shemalperera/RFID_handhed_reader/Images/enclosure/enclosure_bottom.png

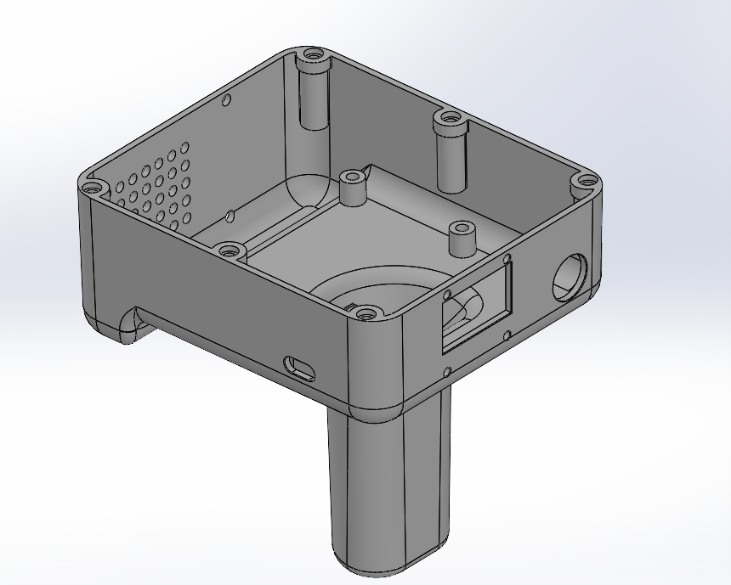
Images/enclosure/enclosure_bottom.png
