shemalperera/RFID_handhed_reader/Images/enclosure/enclosure_hand_sketch.png

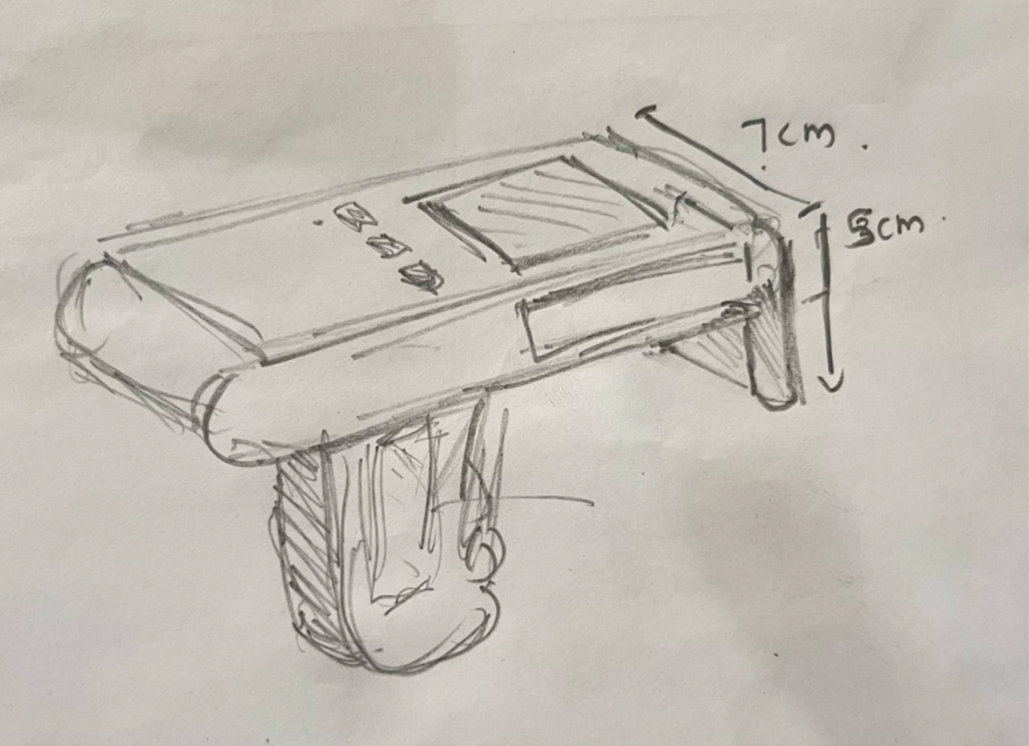
Images/enclosure/enclosure_hand_sketch.png
