shemalperera/RFID_handhed_reader/Images/enclosure/enclosure_lid.png

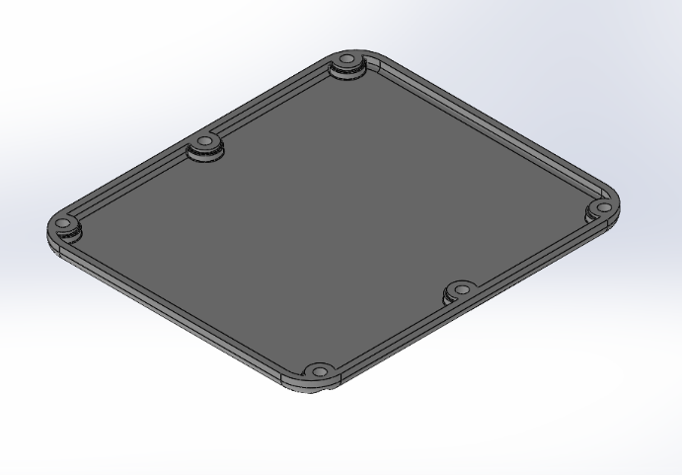
Images/enclosure/enclosure_lid.png
