shemalperera/RFID_handhed_reader/Images/enclosure/mold_bottom.png

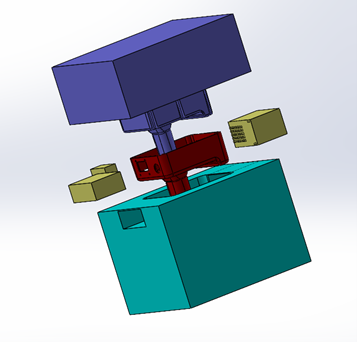
Images/enclosure/mold_bottom.png
