shemalperera/RFID_handhed_reader/Images/enclosure/mold_lid.png

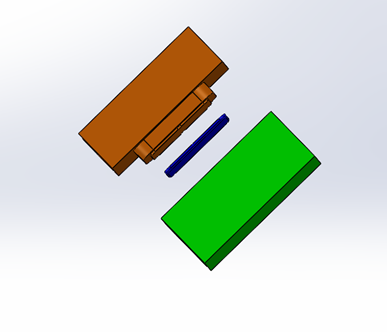
Images/enclosure/mold_lid.png
