shemalperera/RFID_handhed_reader/Images/pcb/main_pcb_front.jpg

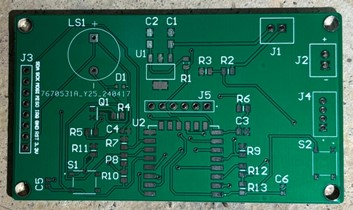
Images/pcb/main_pcb_front.jpg
