shemalperera/RFID_handhed_reader/Images/pcb/main_pcb_rear.jpg

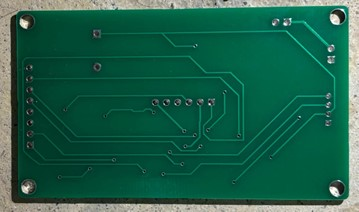
Images/pcb/main_pcb_rear.jpg
