shemalperera/RFID_handhed_reader/Images/pcb/PCB layout.png

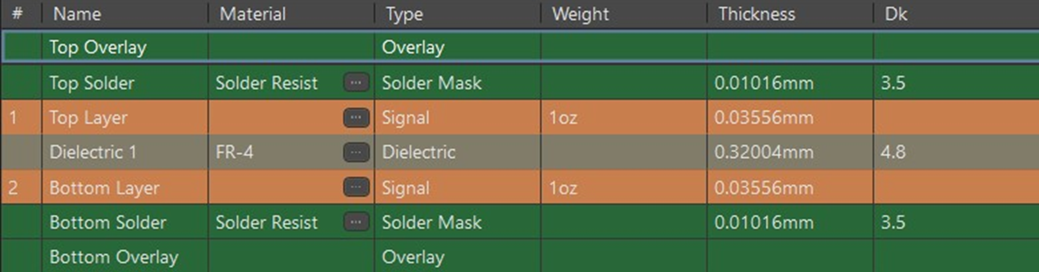
Images/pcb/PCB layout.png
