shemalperera/RFID_handhed_reader/Images/pcb/rfid_bottom_layer.png

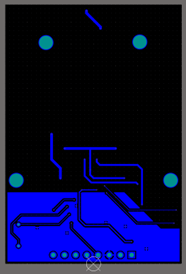
Images/pcb/rfid_bottom_layer.png
