shemalperera/RFID_handhed_reader/Images/pcb/rfid_pcb_rear.jpg

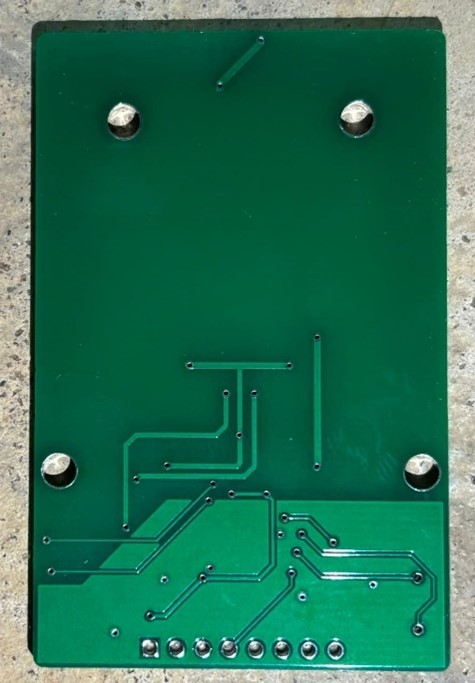
Images/pcb/rfid_pcb_rear.jpg
