shemalperera/RFID_handhed_reader/Images/pcb/rfid_pcb_top.jpg

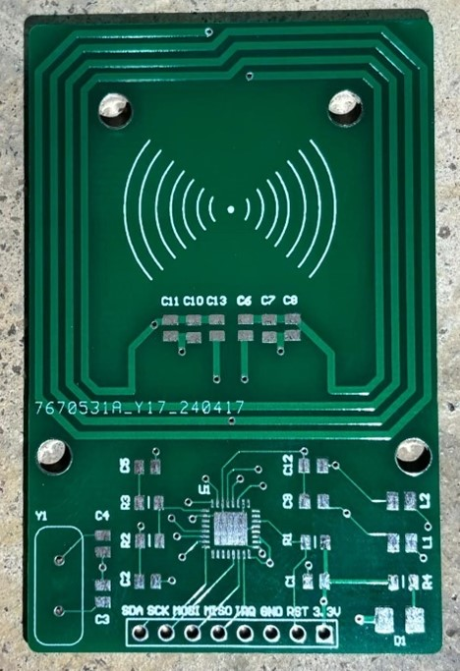
Images/pcb/rfid_pcb_top.jpg
