shemalperera/RFID_handhed_reader/Images/pcb/rfid_top_layer.png

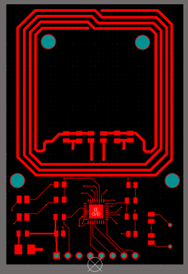
Images/pcb/rfid_top_layer.png
