shemalperera/RFID_handhed_reader/Images/enclosure/enclosure_assembly.png

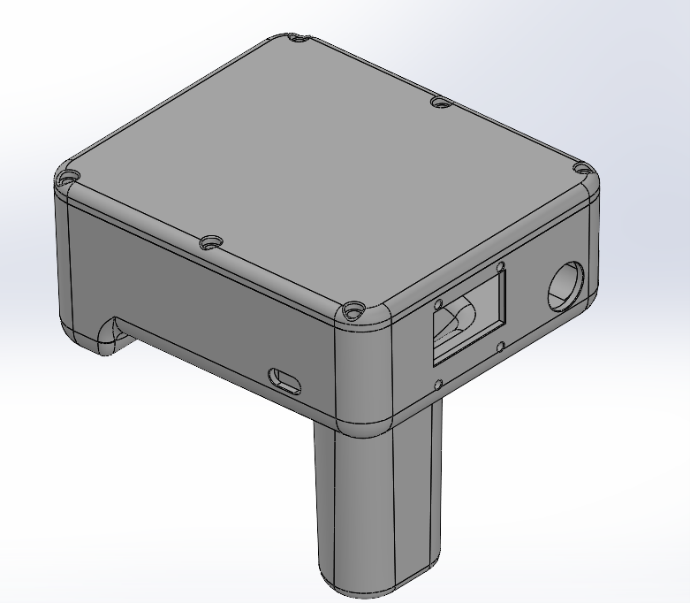
Images/enclosure/enclosure_assembly.png
