shemalperera/RFID_handhed_reader/Images/enclosure/printed_enclosure.png

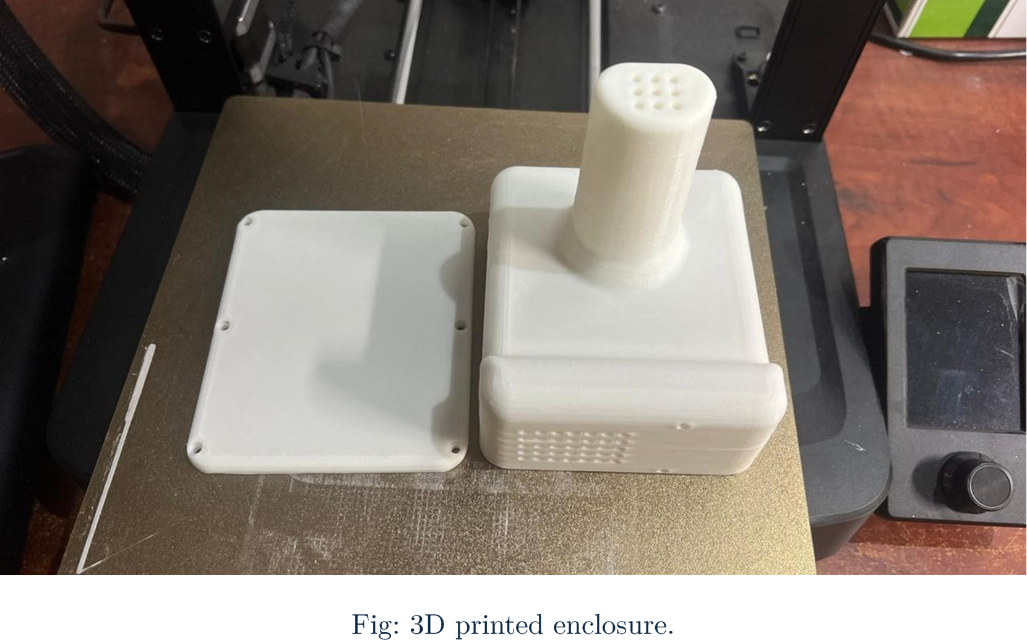
Images/enclosure/printed_enclosure.png
