shemalperera/RFID_handhed_reader/Images/pcb/main_solder_mask.png

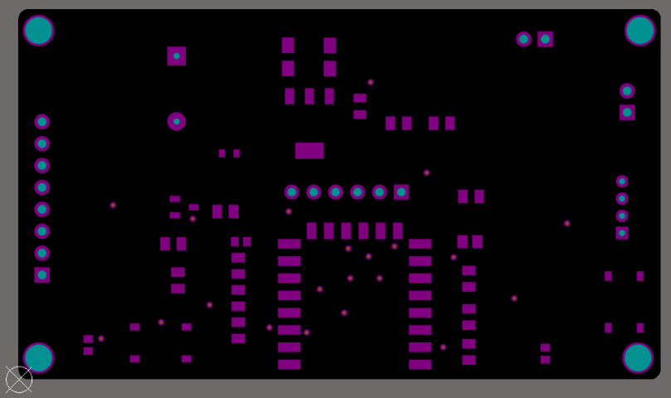
Images/pcb/main_solder_mask.png
