shemalperera/RFID_handhed_reader/Images/pcb/rfid_solder_mask.png

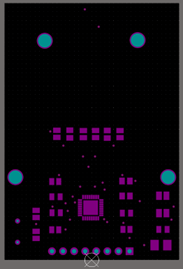
Images/pcb/rfid_solder_mask.png
