shemalperera/RFID_handhed_reader/Images/pcb/soldered_pcb_main.jpg

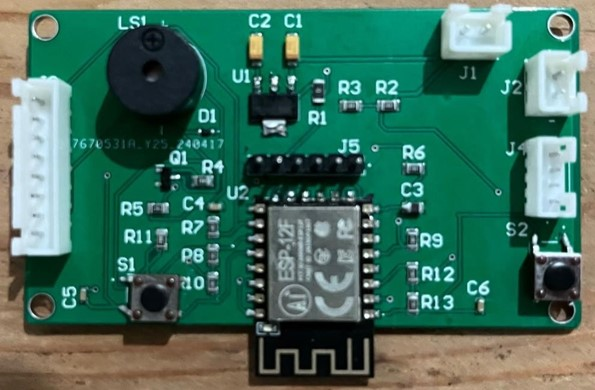
Images/pcb/soldered_pcb_main.jpg
